lu7did/ADX-ddsPIO/doc/ADX-ddsPIO.png

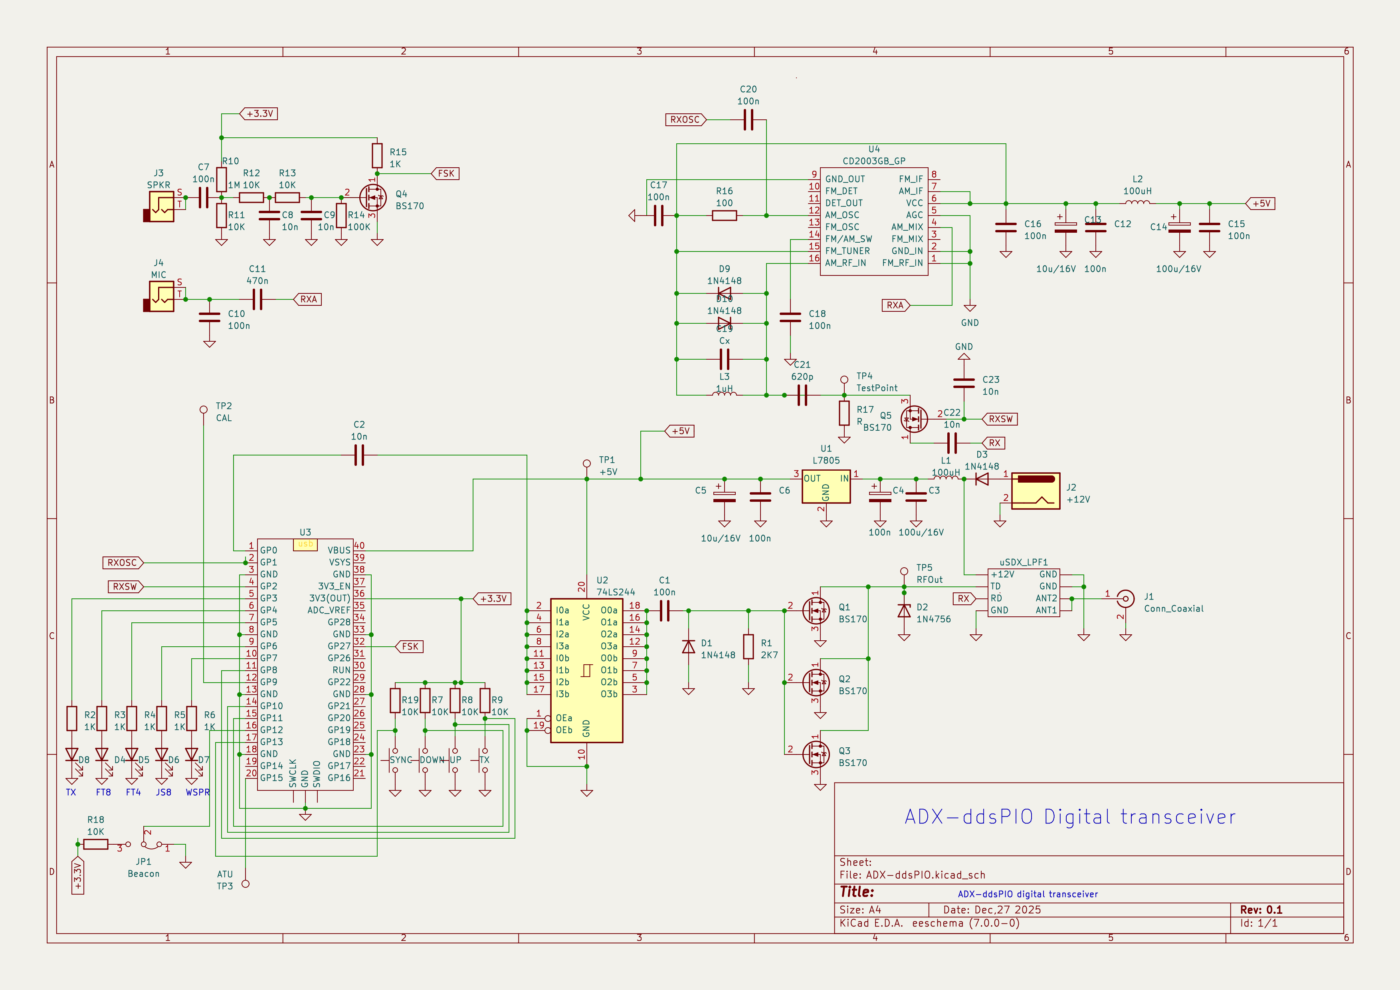
doc/ADX-ddsPIO.png
